microchip-pic-avr-examples/avr128db28-smart-security-sensor-mplab/avr128db28-smart-security-sensor.X/TWI0_host.h

/*
© [2022] Microchip Technology Inc. and its subsidiaries.

    Subject to your compliance with these terms, you may use Microchip 
    software and any derivatives exclusively with Microchip products. 
    You are responsible for complying with 3rd party license terms  
    applicable to your use of 3rd party software (including open source  
    software) that may accompany Microchip software. SOFTWARE IS ?AS IS.? 
    NO WARRANTIES, WHETHER EXPRESS, IMPLIED OR STATUTORY, APPLY TO THIS 
    SOFTWARE, INCLUDING ANY IMPLIED WARRANTIES OF NON-INFRINGEMENT,  
    MERCHANTABILITY, OR FITNESS FOR A PARTICULAR PURPOSE. IN NO EVENT 
    WILL MICROCHIP BE LIABLE FOR ANY INDIRECT, SPECIAL, PUNITIVE, 
    INCIDENTAL OR CONSEQUENTIAL LOSS, DAMAGE, COST OR EXPENSE OF ANY 
    KIND WHATSOEVER RELATED TO THE SOFTWARE, HOWEVER CAUSED, EVEN IF 
    MICROCHIP HAS BEEN ADVISED OF THE POSSIBILITY OR THE DAMAGES ARE 
    FORESEEABLE. TO THE FULLEST EXTENT ALLOWED BY LAW, MICROCHIP?S 
    TOTAL LIABILITY ON ALL CLAIMS RELATED TO THE SOFTWARE WILL NOT 
    EXCEED AMOUNT OF FEES, IF ANY, YOU PAID DIRECTLY TO MICROCHIP FOR 
    THIS SOFTWARE.
*/

#ifndef TWI0_HOST_H
#define	TWI0_HOST_H

#ifdef	__cplusplus
extern "C" {
#endif
    
#include <stdbool.h>
#include <stdint.h>
    
//If defined, internal pullup resistors will be used
//#define TWI0_ENABLE_PULLUPS
    
    /**
     * <b><FONT COLOR=BLUE>void</FONT> TWI0_initHost(<FONT COLOR=BLUE>void</FONT>)</B>
     * 
     * This function initializes the TWI peripheral in Host Mode.
     */
    void TWI0_initHost(void);
    
    /**
     * <b><FONT COLOR=BLUE>void</FONT> TWI0_initPins(<FONT COLOR=BLUE>void</FONT>)</B>
     * 
     * This function initializes the I/O used by the TWI peripheral.
     */
    void TWI0_initPins(void);
    
    /**
     * <b><FONT COLOR=BLUE>void</FONT> TWI0_enable(<FONT COLOR=BLUE>void</FONT>)</B>
     * 
     * This function enables the TWI peripheral and resets the I/O. 
     * Init functions must be called before this function.
     */
    void TWI0_enable(void);
    
    /**
     * <b><FONT COLOR=BLUE>void</FONT> TWI0_disable(<FONT COLOR=BLUE>void</FONT>)</B>
     * 
     * This function disables the TWI peripheral and sets the I/O to OUTPUT HIGH. 
     */
    void TWI0_disable(void);
    
    /**
     * <b><FONT COLOR=BLUE>void</FONT> TWI0_flush(<FONT COLOR=BLUE>void</FONT>)</B>
     * 
     * This function flushes and I2C buffers and resets the peripheral.
     */
    void TWI0_flush(void);

    
    /**
     * <b><FONT COLOR=BLUE>void</FONT> TWI0_sendByte(<FONT COLOR=BLUE>uint8_t</FONT> addr, <FONT COLOR=BLUE>uint8_t</FONT> data)</B>
     * @param uint8_t addr - Client Device Address
     * @param uint8_t data - Data to Send
     * 
     * This function sends a byte of data to the specified address.
     * Returns true if successful, false if it failed
     */
    bool TWI0_sendByte(uint8_t addr, uint8_t data);
    
    /**
     * <b><FONT COLOR=BLUE>void</FONT> TWI0_sendBytes(<FONT COLOR=BLUE>uint8_t</FONT> addr, <FONT COLOR=BLUE>uint8_t</FONT>* data, <FONT COLOR=BLUE>uint8_t</FONT> len)</B>
     * @param uint8_t addr - Client Device Address
     * @param uint8_t* data - Pointer to the data to send
     * @param uint8_t len - Number of Bytes to Send 
     * 
     * This function attempts to send len bytes of data to the client.
     * Returns true if successful, false if it failed
     */
    bool TWI0_sendBytes(uint8_t addr, uint8_t* data, uint8_t len);

    /**
     * <b><FONT COLOR=BLUE>void</FONT> TWI0_readByte(<FONT COLOR=BLUE>uint8_t</FONT> addr, <FONT COLOR=BLUE>uint8_t</FONT> data)</B>
     * @param uint8_t addr - Client Device Address
     * @param uint8_t* data - Where the byte received should be stored
     * 
     * This function attempts to read 1 byte of data from the client.
     * Returns true if successful, fails if unable to get data.
     */
    bool TWI0_readByte(uint8_t addr, uint8_t* data);
    
    /**
     * <b><FONT COLOR=BLUE>void</FONT> TWI0_readBytes(<FONT COLOR=BLUE>uint8_t</FONT> addr, <FONT COLOR=BLUE>uint8_t</FONT>* data, <FONT COLOR=BLUE>uint8_t</FONT> len)</B>
     * @param uint8_t addr - Client Device Address
     * @param uint8_t* data - Where the bytes received should be stored
     * @param uint8_t len - Number of Bytes to Send 
     * 
     * This function attempts to read len bytes of data from the client.
     * Returns true if successful, false if it failed to get data.
     */
    bool TWI0_readBytes(uint8_t addr, uint8_t* data, uint8_t len);
    
    /**
     * <b><FONT COLOR=BLUE>void</FONT> TWI0_sendAndReadBytes(<FONT COLOR=BLUE>uint8_t</FONT> addr, <FONT COLOR=BLUE>uint8_t</FONT> regAddress,<FONT COLOR=BLUE>uint8_t</FONT>* data, <FONT COLOR=BLUE>uint8_t</FONT> len)</B>
     * @param uint8_t addr - Client Device Address
     * @param uint8_t regAddress - Address of Register to Read From
     * @param uint8_t* data - Where the bytes received should be stored
     * @param uint8_t len - Number of Bytes to Send 
     * 
     * This function writes a single byte (regAddress) to the client, then restarts and attempts to read len of data.
     * Returns true if successful, false if it failed to get data.
     */
    bool TWI0_sendAndReadBytes(uint8_t addr, uint8_t regAddress, uint8_t* data, uint8_t len);
    
    /**
     * <b><FONT COLOR=BLUE>void</FONT> TWI0_sendsAndReadBytes(<FONT COLOR=BLUE>uint8_t</FONT> addr, <FONT COLOR=BLUE>uint8_t</FONT>* write, <FONT COLOR=BLUE>uint8_t</FONT> writeLen, <FONT COLOR=BLUE>uint8_t</FONT>* read, <FONT COLOR=BLUE>uint8_t</FONT> readLen)</B>
     * @param uint8_t addr - Client Device Address
     * @param uint8_t* write - Bytes to Write
     * @param uint8_t writeLen - Number of Bytes to write
     * @param uint8_t* read - Where the bytes received should be stored
     * @param uint8_t readLen - Number of Bytes to read 
     * 
     * This function writes writeLen bytes to the client, then restarts and attempts to read readLen of data.
     * Returns true if successful, false if it failed to get data.
     */
    bool TWI0_sendsAndReadBytes(uint8_t addr, uint8_t* write, uint8_t writeLen, uint8_t* read, uint8_t readLen);

    
#ifdef	__cplusplus
}
#endif

#endif	/* TWI0_HOST_H */
